ssDhp/DevBoard_F1C100s/BSP/u-boot-2025.10/doc/develop/pics/flamegraph_zoom.png

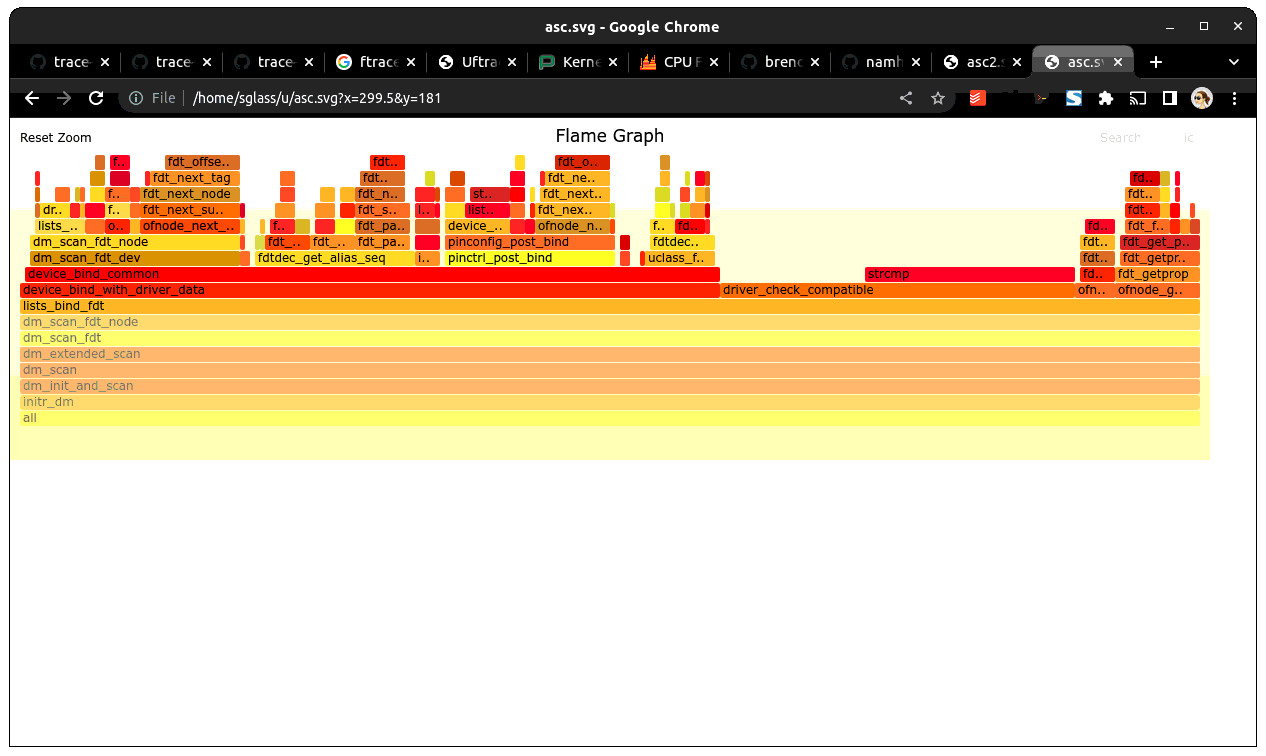
BSP/u-boot-2025.10/doc/develop/pics/flamegraph_zoom.png
