ssDhp/DevBoard_F1C100s/BSP/u-boot-2025.10/doc/develop/pics/kernelshark_fg.png

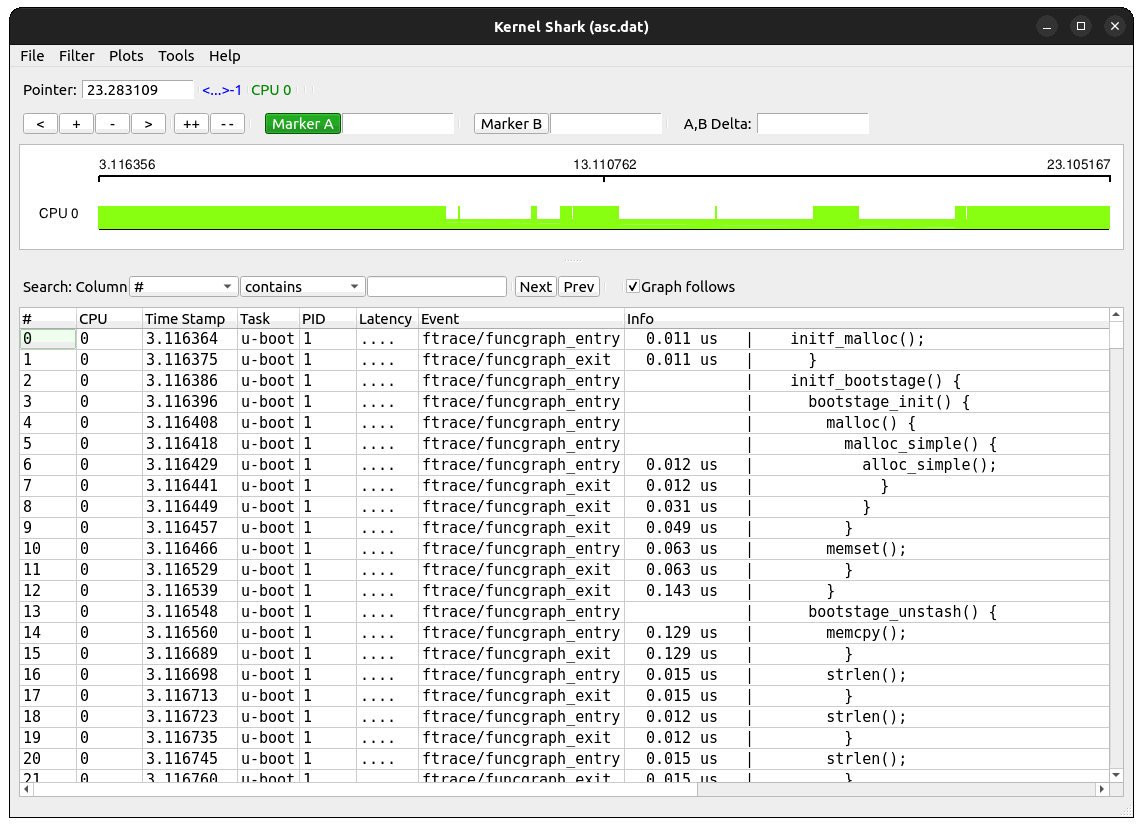
BSP/u-boot-2025.10/doc/develop/pics/kernelshark_fg.png
