ssDhp/DevBoard_F1C100s/BSP/u-boot-2025.10/doc/develop/pics/patman.jpg

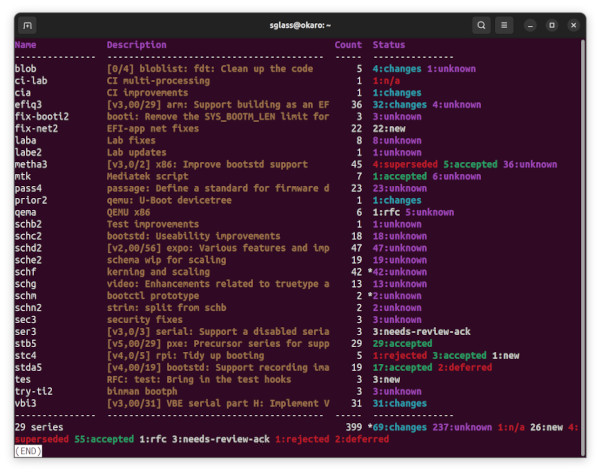
BSP/u-boot-2025.10/doc/develop/pics/patman.jpg
